Cipulot/EC23U/Docs/23U Internals/2 - YnPK2sh.jpg

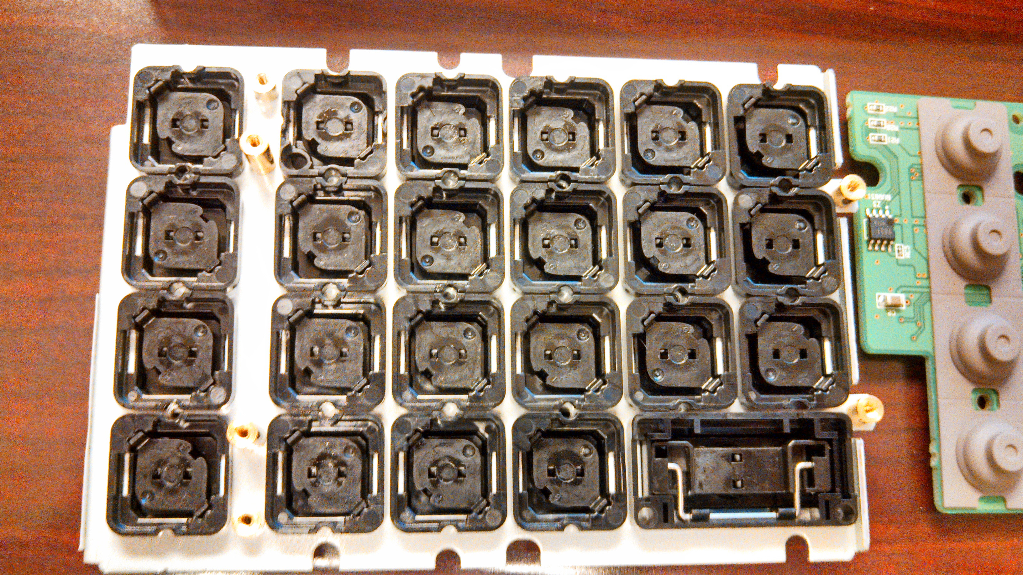
Docs/23U Internals/2 - YnPK2sh.jpg
