Cipulot/EC23U/Docs/23U Internals/8 - 3idQTGp.jpg

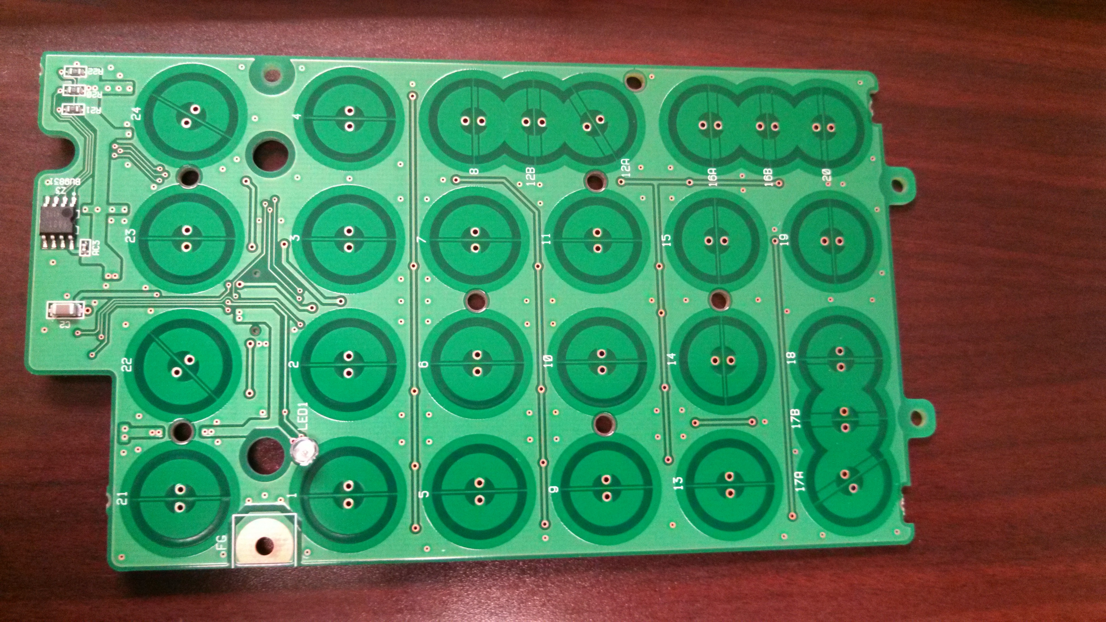
Docs/23U Internals/8 - 3idQTGp.jpg
