Cipulot/EC23U/Docs/23U Internals/9 - vPQrAn1.jpg

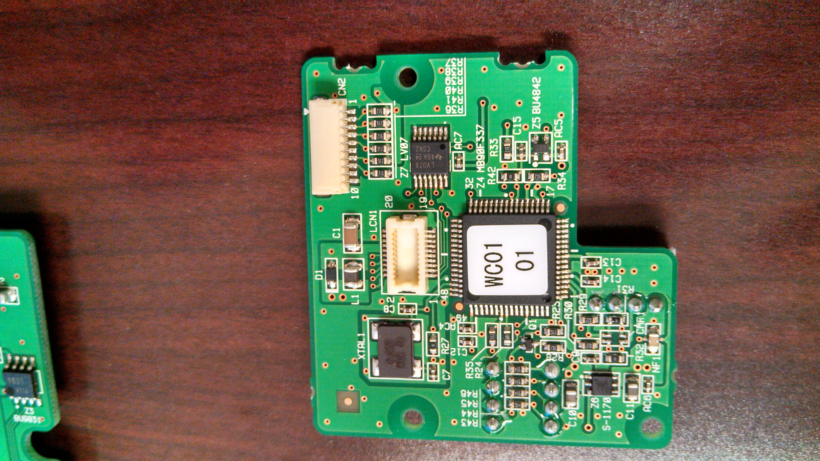
Docs/23U Internals/9 - vPQrAn1.jpg
