Cipulot/EC23U/Docs/23U Internals/12 - vXlalom.jpg

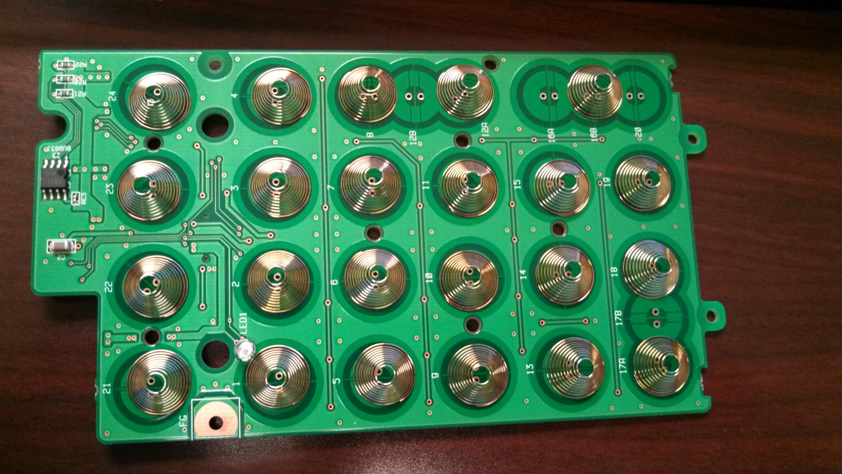
Docs/23U Internals/12 - vXlalom.jpg
